olivierbrcknr/flipdot-communicator/hardware/FlipDotCommunicator/icons.h

int ICON_CUP[] = {0,0,1,1,1,1,1,1,0,0,
                  0,0,1,0,0,0,0,1,1,1,
                  0,0,1,0,0,0,0,1,0,1,
                  0,0,1,0,0,0,0,1,0,1,
                  0,0,1,0,0,0,0,1,1,0,
                  0,0,1,0,0,0,0,1,0,0,
                  0,0,0,1,1,1,1,0,0,0};

int ICON_SAD[] = {0,0,0,0,0,0,0,0,0,0,
                  0,1,1,1,0,0,1,1,1,0,
                  0,1,0,1,0,0,1,0,1,0,
                  0,1,1,1,0,0,1,1,1,0,
                  0,0,0,0,0,0,0,0,0,0,
                  0,0,0,0,1,1,0,0,0,0,
                  0,0,0,1,0,0,1,0,0,0};


int ANIM_STAR_1[] = {0,0,0,0,0,0,0,0,0,0,
                    0,0,0,0,0,0,0,0,0,0,
                    0,0,1,0,0,0,0,0,0,0,
                    0,0,0,0,0,0,0,0,0,0,
                    0,0,0,0,0,0,0,0,0,0,
                    0,0,0,0,0,0,0,0,0,0,
                    0,0,0,0,0,0,0,0,0,0};
int ANIM_STAR_2[] = {0,0,0,0,0,0,0,0,0,0,
                    0,0,1,0,0,0,0,0,0,0,
                    0,1,0,1,0,0,0,0,0,0,
                    0,0,1,0,0,0,0,0,0,0,
                    0,0,0,0,0,0,0,0,0,0,
                    0,0,0,0,0,0,0,0,0,0,
                    0,0,0,0,0,0,0,0,0,0};
int ANIM_STAR_3[] = {0,0,1,0,0,0,0,0,0,0,
                    0,0,0,0,0,0,0,0,0,0,
                    1,0,0,0,1,0,0,0,0,0,
                    0,0,0,0,0,0,0,0,0,0,
                    0,0,1,0,0,0,0,1,0,0,
                    0,0,0,0,0,0,0,0,0,0,
                    0,0,0,0,0,0,0,0,0,0};
int ANIM_STAR_4[] = {0,0,0,0,0,0,0,0,0,0,
                    0,0,0,0,0,0,0,0,0,0,
                    0,0,0,0,0,0,0,0,0,0,
                    0,0,0,0,0,0,0,1,0,0,
                    0,0,0,0,0,0,1,0,1,0,
                    0,0,0,0,0,0,0,1,0,0,
                    0,0,0,0,0,0,0,0,0,0};
int ANIM_STAR_5[] = {0,0,0,0,0,0,0,0,0,0,
                    0,0,0,0,0,0,0,0,0,0,
                    0,0,0,0,0,0,0,1,0,0,
                    0,0,0,0,0,0,0,0,0,0,
                    0,0,0,0,0,1,0,0,0,1,
                    0,0,0,0,0,0,0,0,0,0,
                    0,0,0,0,0,0,0,1,0,0};
